crazy-hair/roachslimes/docs/images/pcbnew_2024-10-07_12-25-07.png

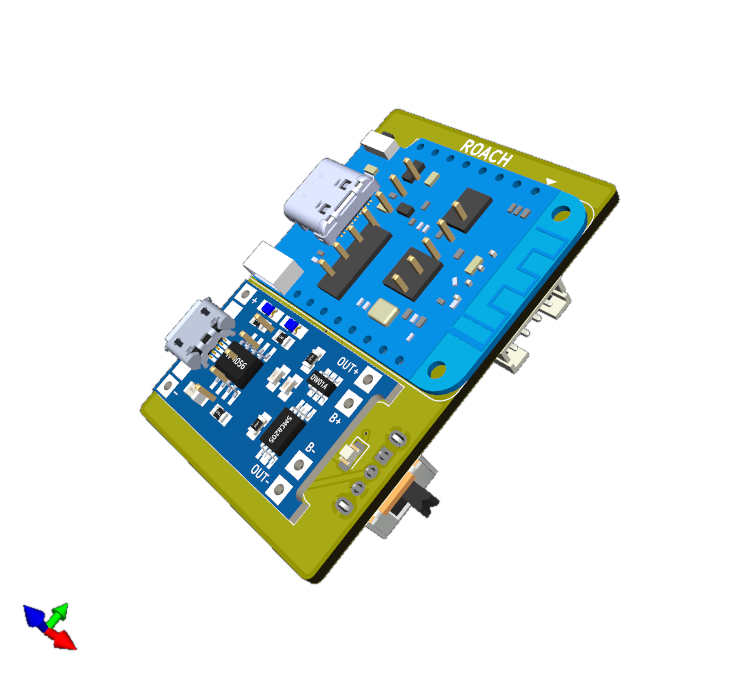
docs/images/pcbnew_2024-10-07_12-25-07.png
